sergipacheco55/Dijous_D_Combustible/Simulacions/Díode de protecció.asc

D1: diode; 1N5408
D2: diode; 1N5408
L1: ind; 33µ
L2: ind; 1m
Q1: npn
R1: res; 4,7k
R2: res; 50
R3: res; 5
S1: sw
V1: voltage; PULSE(0 5 0 1u 1u 5m 10m)
V2: voltage; 12
V3: voltage; 12
V4: voltage; PULSE(0 5 0 1u 1u 5m 10m)
Named nets: 0
.model 1N5408 D(IS=200n RS=0.025 N=1.45 BV=1000 IBV=5u Cjo=50p M=0.33 VJ=0.7)
.tran 50m
.model SW VSWITCH(VON=3V VOFF=0V RON=0.1 ROFF=1Meg)
