sergipacheco55/Dijous_D_Combustible/Simulacions/Regulador de tensió.asc

C1: cap; 470µ
C2: cap; 220µ
C3: cap; 1n
C4: cap; 10µ
C5: cap; 22µ
D1: diode; DMBR340
D2: diode; D1N5822
L1: ind; 68µ
R1: res; 1k
R2: res; 4.7k
R3: res; 1k
U1: LM2596_ADJ2
U2: LT1117-5
V1: voltage; 12
Named nets: 0, Vout
.model D1N5822 D(IS=5u RS=0.02 CJO=300p M=0.33 VJ=0.3 TT=8n BV=40 IBV=0.5m N=1.05)
.model DMBR340 D(IS=6u RS=0.025 CJO=250p M=0.33 VJ=0.3 TT=6n BV=40 IBV=0.5m N=1.08)
.tran 0 20m 0 0.1m
